uriba107/fcc_controller/src/Controller/Fcc3/Joystick.h

/*
             LUFA Library
     Copyright (C) Dean Camera, 2015.

  dean [at] fourwalledcubicle [dot] com
           www.lufa-lib.org
*/

/*
  Copyright 2015  Dean Camera (dean [at] fourwalledcubicle [dot] com)

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
  The author disclaims all warranties with regard to this
  software, including all implied warranties of merchantability
  and fitness.  In no event shall the author be liable for any
  special, indirect or consequential damages or any damages
  whatsoever resulting from loss of use, data or profits, whether
  in an action of contract, negligence or other tortious action,
  arising out of or in connection with the use or performance of
  this software.
*/

/** \file
 *
 *  Header file for Joystick.c.
 */

#ifndef _JOYSTICK_H_
#define _JOYSTICK_H_

	/* Includes: */
		#include <avr/io.h>
		#include <avr/wdt.h>
		#include <avr/power.h>
		#include <avr/interrupt.h>
		#include <string.h>

		#include "Descriptors.h"

		#include <LUFA/Drivers/USB/USB.h>
		#include <LUFA/Drivers/Board/Joystick.h>
		#include <LUFA/Drivers/Board/LEDs.h>
		#include <LUFA/Drivers/Board/Buttons.h>
		#include <LUFA/Platform/Platform.h>

		#include "fcc3.h"

	/* Macros: */
			/** HID Class specific request to get the next HID report from the device. */
			#define REQ_GetReport             0x01

			/** HID Class specific request to send the next HID report to the device. */
			#define REQ_SetReport             0x09

		/** LED mask for the library LED driver, to indicate that the USB interface is not ready. */
		#define LEDMASK_USB_NOTREADY      LEDS_LED1

		/** LED mask for the library LED driver, to indicate that the USB interface is enumerating. */
		#define LEDMASK_USB_ENUMERATING  (LEDS_LED2 | LEDS_LED3)

		/** LED mask for the library LED driver, to indicate that the USB interface is ready. */
		#define LEDMASK_USB_READY        (LEDS_LED2 | LEDS_LED4)

		/** LED mask for the library LED driver, to indicate that an error has occurred in the USB interface. */
		#define LEDMASK_USB_ERROR        (LEDS_LED1 | LEDS_LED3)

	/* Type Defines: */
		/** Type define for the joystick HID report structure, for creating and sending HID reports to the host PC.
		 *  This mirrors the layout described to the host in the HID report descriptor, in Descriptors.c.
		 */
		typedef struct USB_JoystickReport_Data_t
		{
			int16_t  X:11; /**< Current absolute joystick X position, as a signed 8-bit integer */
			int16_t  Y:11; /**< Current absolute joystick Y position, as a signed 8-bit integer */
			uint8_t Hat:4; /** <Bit Mast of the currently pressed Hat direction */
			uint32_t Buttons:19; /**< Bit mask of the currently pressed joystick buttons */
			uint8_t CurrentOptions;
			int16_t CurrentUserDef;
		} USB_JoystickReport_Data_t;

    /* Glabal Vars */
	// extern bool JoystickRunning;

	/* Function Prototypes: */
		void SetupHardware(void);
		void HID_Task(void);

		void EVENT_USB_Device_Connect(void);
		void EVENT_USB_Device_Disconnect(void);
		void EVENT_USB_Device_ConfigurationChanged(void);
		void EVENT_USB_Device_ControlRequest(void);
		void EVENT_USB_Device_UnhandledControlRequest(void);

		bool GetNextReport(USB_JoystickReport_Data_t* const ReportData);

#endif
